dpaschal/tarpn-node/hardware/enclosure/stl/vented-53mm-jul16-1.stl

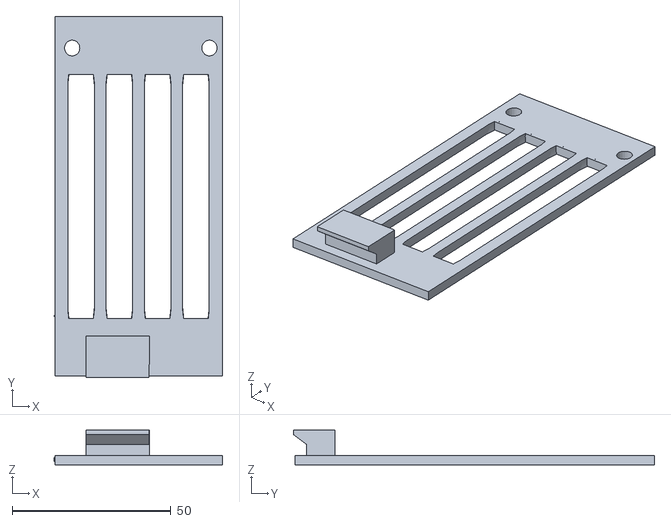
[picture p15: CAD file, 2026-01-13]
hardware/enclosure/stl/vented-53mm-jul16-1.stl
53.0 x 113.8 x 11.0
