dpaschal/tarpn-node/hardware/enclosure/stl/hdmi-and-usb-big-socket-hole-2025apr03-1.stl

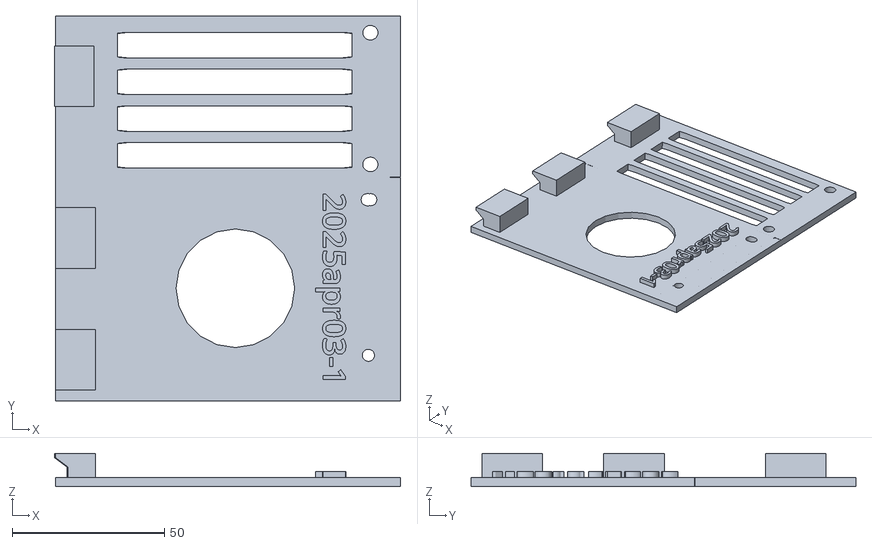
[picture p16: CAD file, 2026-01-13]
hardware/enclosure/stl/hdmi-and-usb-big-socket-hole-2025apr03-1.stl
113.8 x 126.6 x 11.0
