dpaschal/tarpn-node/hardware/enclosure/stl/corners_and_beams.3mf

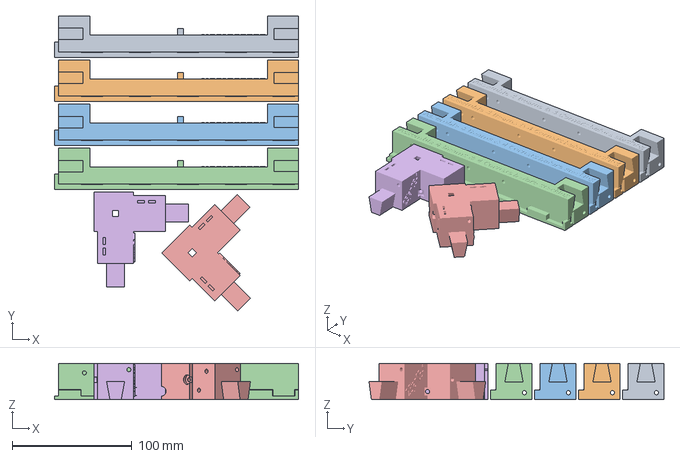
[picture p17: CAD file, 2026-01-13]
hardware/enclosure/stl/corners_and_beams.3mf
203.7 x 246.0 x 30.3 mm
beam-2025apr25-1.stl x 4
roof-corner-25jan03-1.stl x 2
