dpaschal/tarpn-node/hardware/enclosure/stl/power-supply-panel-25feb01-1.stl

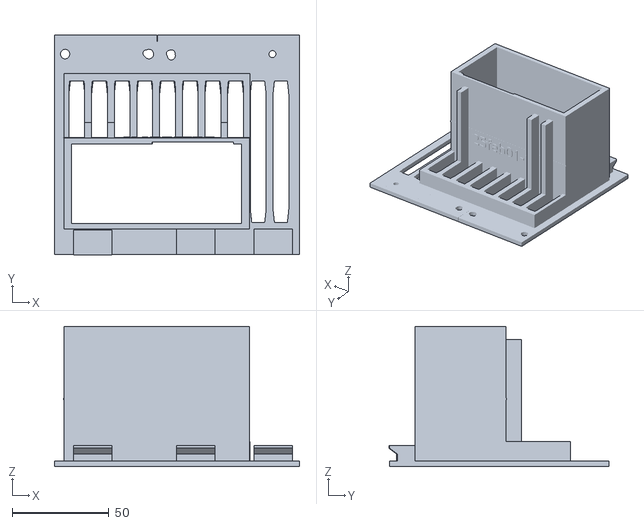
[picture p18: CAD file, 2026-01-13]
hardware/enclosure/stl/power-supply-panel-25feb01-1.stl
126.6 x 113.8 x 72.5
