dpaschal/tarpn-node/hardware/enclosure/stl/ninotnc-vertical-a4-tray-2025apr30-1.stl

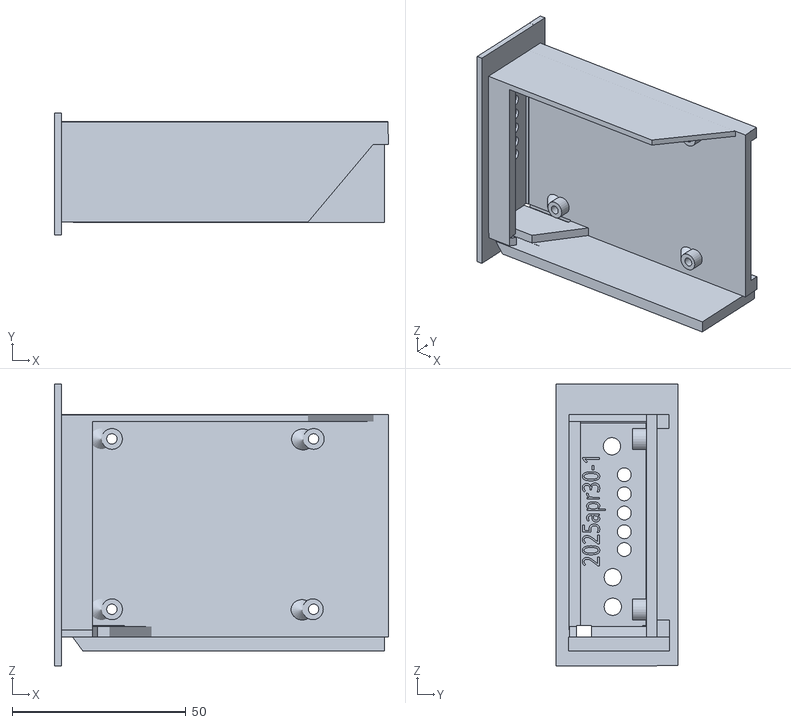
[picture p19: CAD file, 2026-01-13]
hardware/enclosure/stl/ninotnc-vertical-a4-tray-2025apr30-1.stl
96.0 x 35.1 x 81.1
