dpaschal/tarpn-node/hardware/enclosure/stl/fuse-holder-2025apr12-2.stl

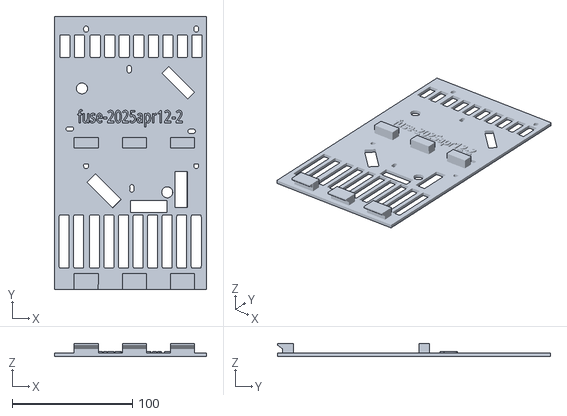
[picture p20: CAD file, 2026-01-13]
hardware/enclosure/stl/fuse-holder-2025apr12-2.stl
126.5 x 226.8 x 11.0
