dpaschal/tarpn-node/hardware/enclosure/stl/control-panel-25may27-2.stl

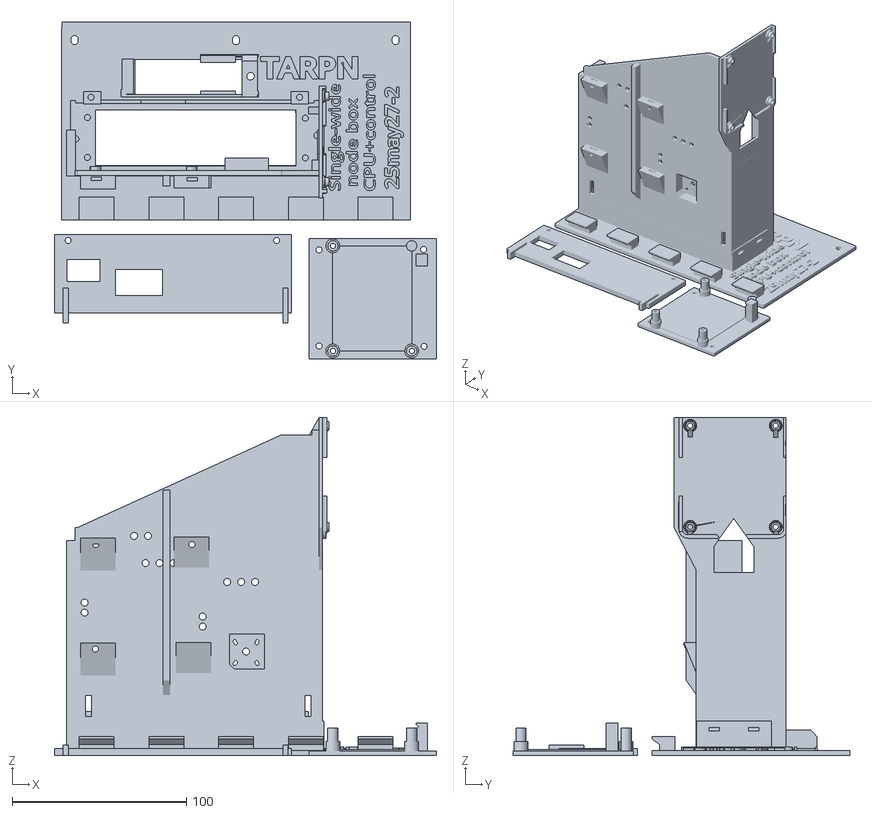
[picture p21: CAD file, 2026-01-13]
hardware/enclosure/stl/control-panel-25may27-2.stl
219.0 x 193.3 x 194.0
