dpaschal/tarpn-node/hardware/enclosure/stl/side-panel-jul09-1.stl

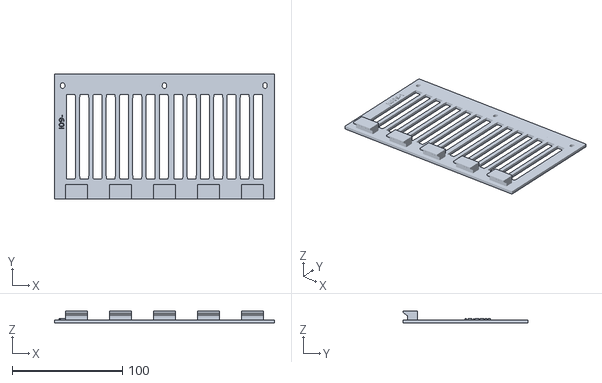
[picture p22: CAD file, 2026-01-13]
hardware/enclosure/stl/side-panel-jul09-1.stl
200.0 x 113.4 x 11.0
