dpaschal/tarpn-node/hardware/enclosure/stl/ninotnc-tray-handle-2025apr28-2.stl

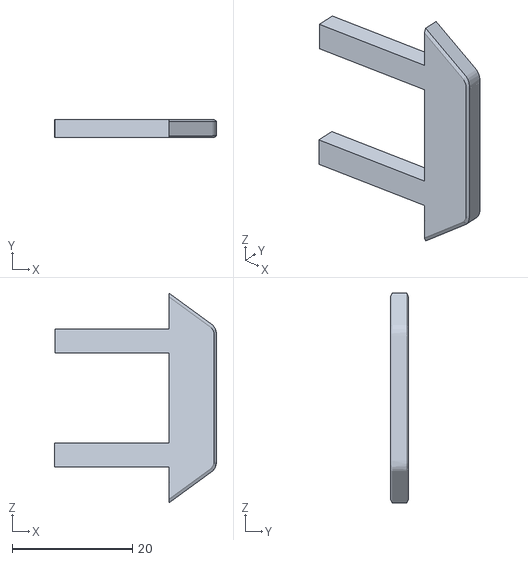
[picture p23: CAD file, 2026-01-13]
hardware/enclosure/stl/ninotnc-tray-handle-2025apr28-2.stl
27.0 x 3.01 x 34.9
