dpaschal/tarpn-node/hardware/enclosure/stl/roof-quadrant-25jan05-1.stl

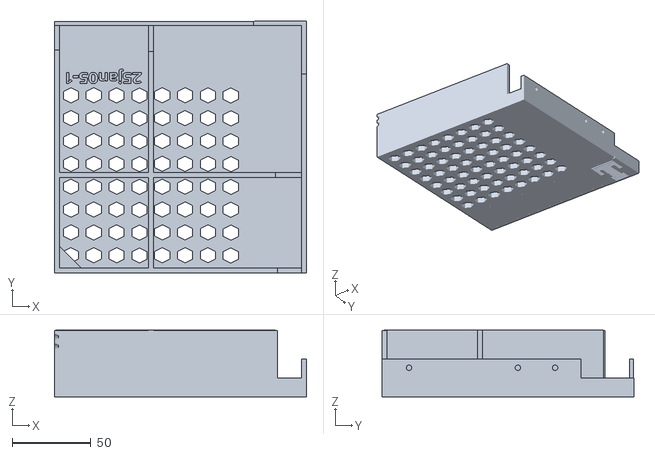
[picture p24: CAD file, 2026-01-13]
hardware/enclosure/stl/roof-quadrant-25jan05-1.stl
159.6 x 159.8 x 42.2
