dpaschal/tarpn-node/hardware/enclosure/stl/right-half-panel-aug01-2.stl

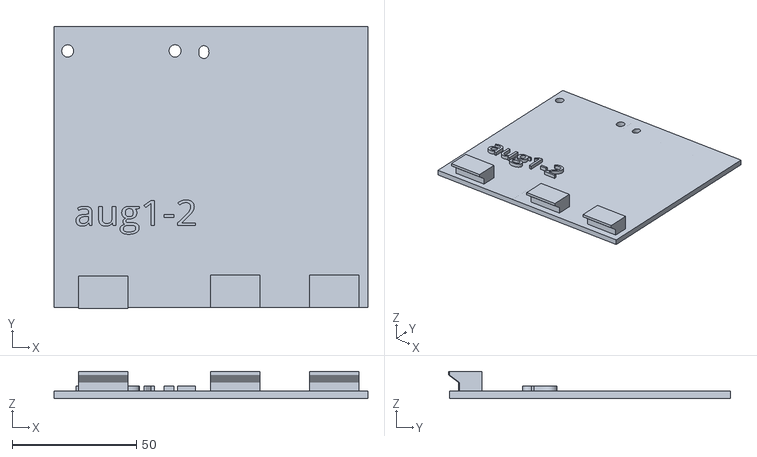
[picture p25: CAD file, 2026-01-13]
hardware/enclosure/stl/right-half-panel-aug01-2.stl
126.6 x 113.8 x 11.0
