dpaschal/tarpn-node/hardware/enclosure/stl/bottom-panel-key.stl

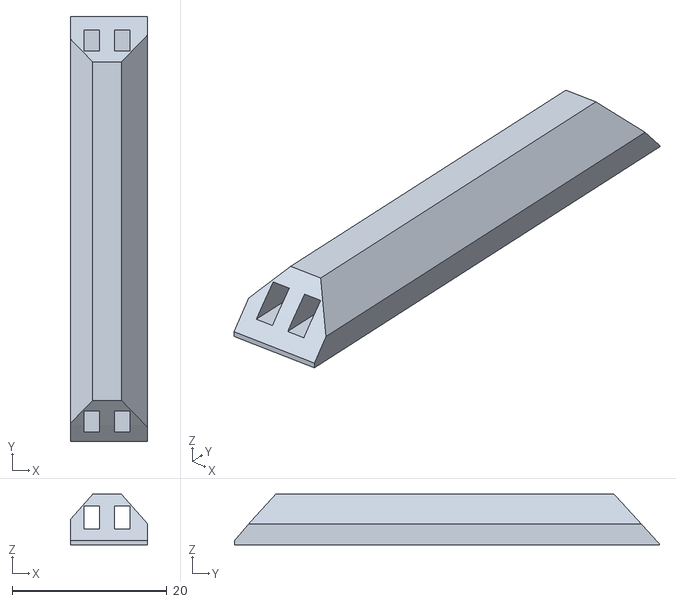
[picture p26: CAD file, 2026-01-13]
hardware/enclosure/stl/bottom-panel-key.stl
10.0 x 55.0 x 6.54
