dpaschal/tarpn-node/hardware/enclosure/stl/corner-tower-T2025may01-1.stl

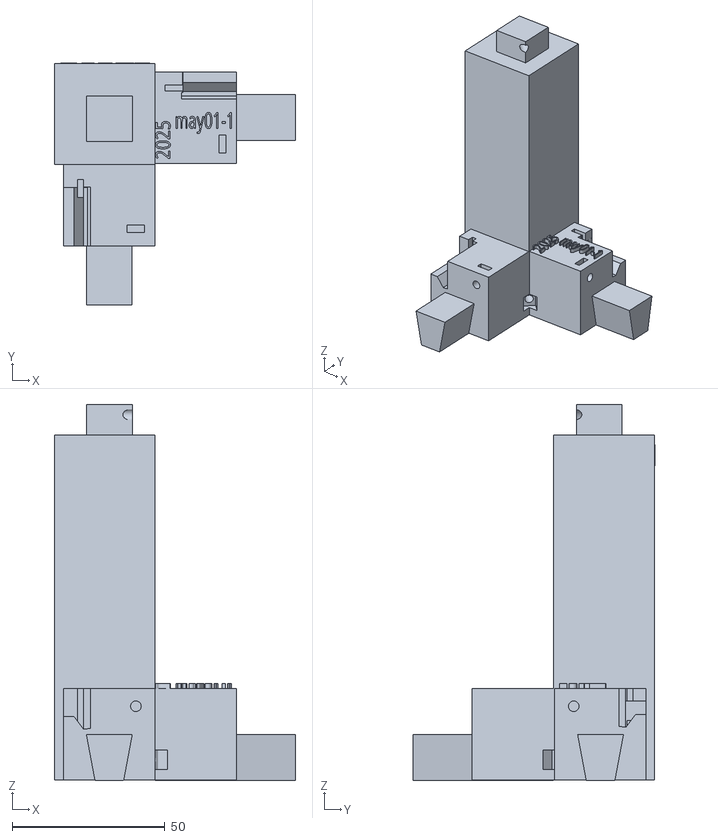
[picture p27: CAD file, 2026-01-13]
hardware/enclosure/stl/corner-tower-T2025may01-1.stl
79.0 x 79.4 x 123.1
