dpaschal/tarpn-node/hardware/enclosure/stl/coax-hole-53mm-25jan02-1.stl

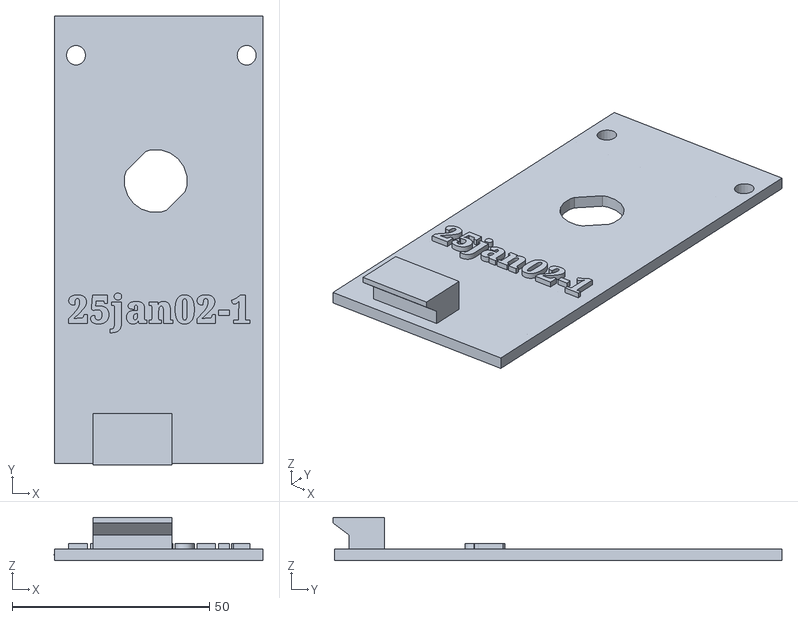
[picture p28: CAD file, 2026-01-13]
hardware/enclosure/stl/coax-hole-53mm-25jan02-1.stl
53.0 x 113.8 x 11.0
