dpaschal/tarpn-node/hardware/enclosure/stl/bottom-panel-stephen-2024sep05-1.stl

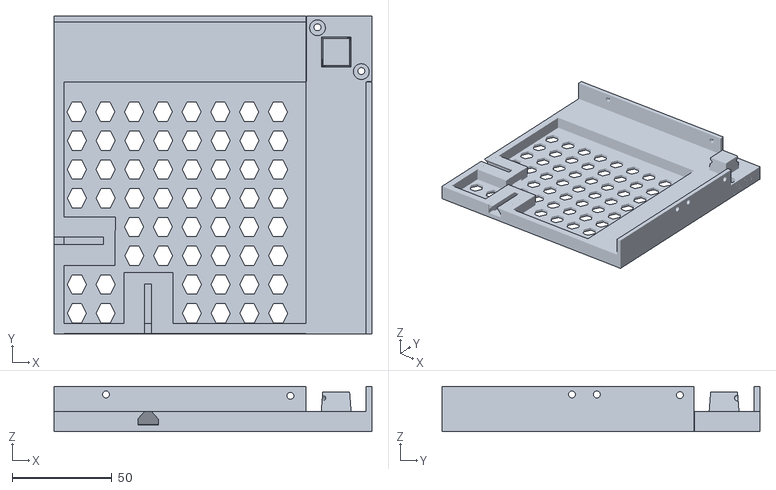
[picture p29: CAD file, 2026-01-13]
hardware/enclosure/stl/bottom-panel-stephen-2024sep05-1.stl
159.7 x 159.7 x 22.7
