dpaschal/tarpn-node/hardware/enclosure/stl/power-supply-support-2025mar21-3.stl

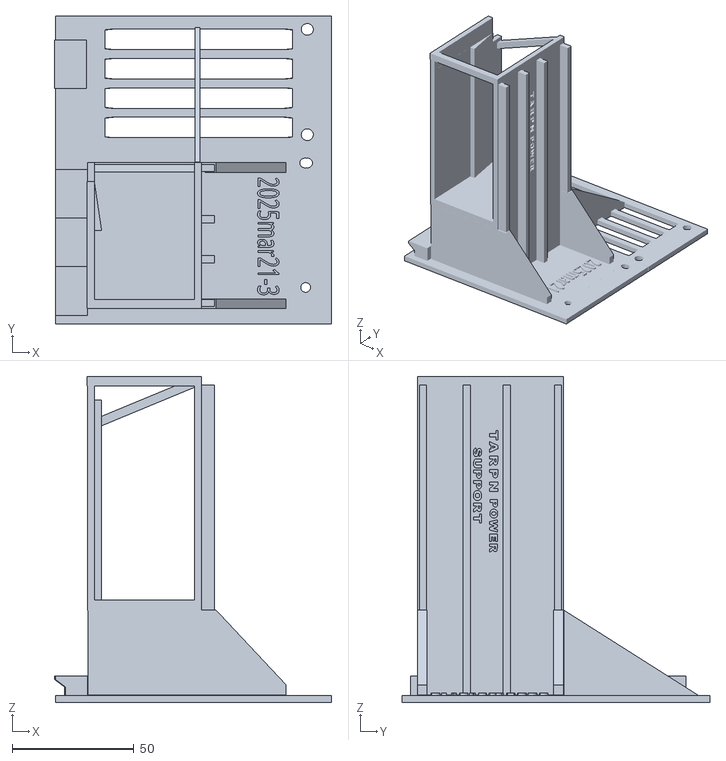
[picture p30: CAD file, 2026-01-13]
hardware/enclosure/stl/power-supply-support-2025mar21-3.stl
113.8 x 126.6 x 134.2
