dpaschal/tarpn-node/hardware/enclosure/stl/hinged-200mm-panel-2025may23-1.stl

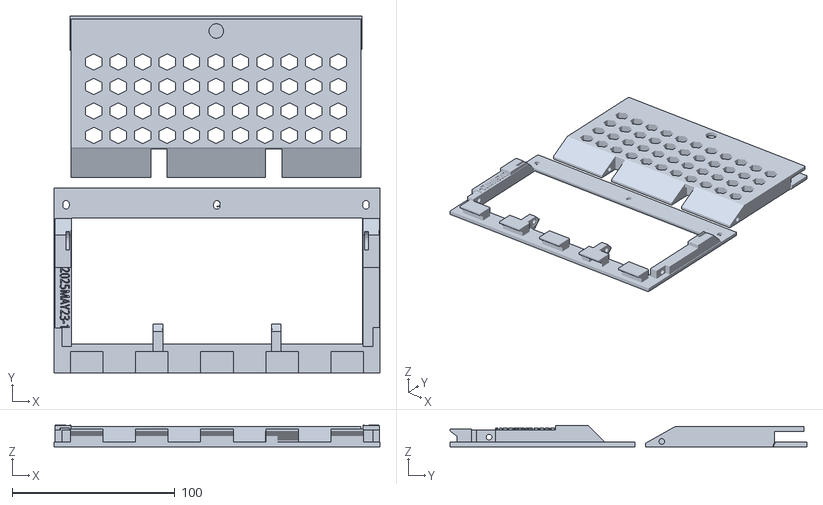
[picture p31: CAD file, 2026-01-13]
hardware/enclosure/stl/hinged-200mm-panel-2025may23-1.stl
200.0 x 218.7 x 13.2
